MKrysz/pullup_counter/pullup_counter_code/Core/Src/images.c

#include "images.h"
#include "ssd1306.h"

#define NEEDLE_SIZE 21

/**
 * @brief 
 * 
 * @param x 
 * @param y 
 * @param image 
 */
void Image_Draw(uint8_t x, uint8_t y, image_t image)
{
    for(size_t i = 0; i<image.size; i++){
        uint8_t tempX, tempY;
        tempX = image.data[i*2];
        tempY = image.data[i*2+1];
        ssd1306_DrawPixel(x+tempX, y+tempY, White);
    }
}

void Image_Clear(uint8_t x, uint8_t y, image_t image)
{

    for(size_t i = 0; i<image.size; i++){
        uint8_t tempX, tempY;
        tempX = image.data[i*2];
        tempY = image.data[i*2+1];
        ssd1306_DrawPixel(x+tempX, y+tempY, Black);
    }
}

static const uint8_t img_meter_data[] = {
    0,26,  0,25,  0,24,  0,23,  0,22,  0,21,  1,20,  1,19,  1,18,  1,17,  2,16,  2,15,  
    2,14,  3,13,  3,12,  3,11,  4,10,  4,9,   5,8,   5,7,   6,6,   7,5,   8,5,   9,4,   
    10,4,  11,3,  12,3,  13,3,  14,2,  15,2,  16,2,  17,1,  18,1,  19,1,  20,1,  21,0, 
    22,0,  23,0,  24,0,  25,0,  26,0,  27,0,  28,0,  29,1,  30,1,  31,1,  32,1,  33,2, 
    34,2,  35,2,  36,3,  37,3,  38,3,  39,4,  40,4,  41,5,  42,5,  43,6,  44,7,  44,8,  
    45,9,  45,10, 46,11, 46,12, 46,13, 47,14, 47,15, 47,16, 48,17, 48,18, 48,19, 48,20, 
    49,21, 49,22, 49,23, 49,24, 49,25, 49,26, 23,25, 24,25, 24,24, 25,24, 25,25, 26,25,
    0,26,  1,26,  2,26,  3,26,  4,26,  5,26,  6,26,  7,26,  8,26,  9,26,  10,26, 11,26, 
    12,26, 13,26, 14,26, 15,26, 16,26, 17,26, 18,26, 19,26, 20,26, 21,26, 22,26, 23,26, 
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

        for(size_t i = 0; i<NEEDLE_SIZE; i++){
            uint8_t tempX, tempY;
            tempX = img_meter.Xsize - img_meterNeedle_data[idx][i*2];
            tempY = img_meterNeedle_data[idx][i*2+1];
            ssd1306_DrawPixel(x+tempX, y+tempY, color);
        }
    }
}

/**
 * @brief 
 * 
 * @param x 
 * @param y 
 * @param idx max 67
 */
void Image_DrawNeedle(uint8_t x, uint8_t y, size_t idx)
{
    static uint8_t last_idx = 0;

    if(idx >= 68)
        idx = 67;
        
    _DrawNeedle(x, y, last_idx, Black);
    _DrawNeedle(x, y, idx, White);
    last_idx = idx;
}
