MKrysz/pullup_counter/pullup_counter_code/Core/Src/adc.c

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
/* Includes ------------------------------------------------------------------*/
#include "adc.h"

/* USER CODE BEGIN 0 */
#include "settings.h"
/* USER CODE END 0 */

ADC_HandleTypeDef hadc1;
DMA_HandleTypeDef hdma_adc1;

/* ADC1 init function */
void MX_ADC1_Init(void)
{

  ADC_ChannelConfTypeDef sConfig = {0};

  /** Configure the global features of the ADC (Clock, Resolution, Data Alignment and number of conversion)
  */
  hadc1.Instance = ADC1;
  hadc1.Init.ClockPrescaler = ADC_CLOCK_SYNC_PCLK_DIV2;
  hadc1.Init.Resolution = ADC_RESOLUTION_12B;
  hadc1.Init.DataAlign = ADC_DATAALIGN_RIGHT;
  hadc1.Init.ScanConvMode = ADC_SCAN_ENABLE;
  hadc1.Init.EOCSelection = ADC_EOC_SEQ_CONV;
  hadc1.Init.LowPowerAutoWait = DISABLE;
  hadc1.Init.LowPowerAutoPowerOff = DISABLE;
  hadc1.Init.ContinuousConvMode = ENABLE;
  hadc1.Init.NbrOfConversion = 3;
  hadc1.Init.ExternalTrigConv = ADC_SOFTWARE_START;
  hadc1.Init.ExternalTrigConvEdge = ADC_EXTERNALTRIGCONVEDGE_NONE;
  hadc1.Init.DMAContinuousRequests = ENABLE;
  hadc1.Init.Overrun = ADC_OVR_DATA_PRESERVED;
  hadc1.Init.SamplingTimeCommon1 = ADC_SAMPLETIME_160CYCLES_5;
  hadc1.Init.SamplingTimeCommon2 = ADC_SAMPLETIME_1CYCLE_5;
  hadc1.Init.OversamplingMode = DISABLE;
  hadc1.Init.TriggerFrequencyMode = ADC_TRIGGER_FREQ_HIGH;
  if (HAL_ADC_Init(&hadc1) != HAL_OK)
  {
    Error_Handler();
  }

  /** Configure Regular Channel
  */
  sConfig.Channel = ADC_CHANNEL_0;
  sConfig.Rank = ADC_REGULAR_RANK_1;
  sConfig.SamplingTime = ADC_SAMPLINGTIME_COMMON_1;
  if (HAL_ADC_ConfigChannel(&hadc1, &sConfig) != HAL_OK)
  {
    Error_Handler();
  }

  /** Configure Regular Channel
  */
  sConfig.Channel = ADC_CHANNEL_1;
  sConfig.Rank = ADC_REGULAR_RANK_2;
  if (HAL_ADC_ConfigChannel(&hadc1, &sConfig) != HAL_OK)
  {
    Error_Handler();
  }

  /** Configure Regular Channel
  */
  sConfig.Channel = ADC_CHANNEL_VBAT;
  sConfig.Rank = ADC_REGULAR_RANK_3;
  if (HAL_ADC_ConfigChannel(&hadc1, &sConfig) != HAL_OK)
  {
    Error_Handler();
  }
}

void HAL_ADC_MspInit(ADC_HandleTypeDef* adcHandle)
{

  GPIO_InitTypeDef GPIO_InitStruct = {0};
  if(adcHandle->Instance==ADC1)
  {
    /* ADC1 clock enable */
    __HAL_RCC_ADC_CLK_ENABLE();

    __HAL_RCC_GPIOA_CLK_ENABLE();
    /**ADC1 GPIO Configuration
    PA0     ------> ADC1_IN0
    PA1     ------> ADC1_IN1
    */
    GPIO_InitStruct.Pin = PROX_OUT_Pin|BAT_RAW_Pin;
    GPIO_InitStruct.Mode = GPIO_MODE_ANALOG;
    GPIO_InitStruct.Pull = GPIO_NOPULL;
    HAL_GPIO_Init(GPIOA, &GPIO_InitStruct);

    /* ADC1 DMA Init */
    /* ADC1 Init */
    hdma_adc1.Instance = DMA1_Channel2;
    hdma_adc1.Init.Request = DMA_REQUEST_ADC1;
    hdma_adc1.Init.Direction = DMA_PERIPH_TO_MEMORY;
    hdma_adc1.Init.PeriphInc = DMA_PINC_DISABLE;
    hdma_adc1.Init.MemInc = DMA_MINC_ENABLE;
    hdma_adc1.Init.PeriphDataAlignment = DMA_PDATAALIGN_WORD;
    hdma_adc1.Init.MemDataAlignment = DMA_MDATAALIGN_WORD;
    hdma_adc1.Init.Mode = DMA_CIRCULAR;
    hdma_adc1.Init.Priority = DMA_PRIORITY_LOW;
    if (HAL_DMA_Init(&hdma_adc1) != HAL_OK)
    {
      Error_Handler();
    }

    __HAL_LINKDMA(adcHandle,DMA_Handle,hdma_adc1);

  }
}

void HAL_ADC_MspDeInit(ADC_HandleTypeDef* adcHandle)
{

  if(adcHandle->Instance==ADC1)
  {
    /* Peripheral clock disable */
    __HAL_RCC_ADC_CLK_DISABLE();

    /**ADC1 GPIO Configuration
    PA0     ------> ADC1_IN0
    PA1     ------> ADC1_IN1
    */
    HAL_GPIO_DeInit(GPIOA, PROX_OUT_Pin|BAT_RAW_Pin);

    /* ADC1 DMA DeInit */
    HAL_DMA_DeInit(adcHandle->DMA_Handle);
  }
}

/* USER CODE BEGIN 1 */

uint32_t ambientDistance = 0;

/**
 * [0] - Poximity
 * [1] - Battery
 * [2] - Backup battery
 */
uint32_t ADC_buffer[3];

void ADC_Init()
{
  HAL_ADC_Start_DMA(&hadc1, ADC_buffer, 3);
}


/**
 * @brief returns relative reading from proximity sensor
 * 
 * @return uint32_t differnce between ambient and current voltage
 */
int32_t ADC_MeasureDistance()
{
  uint32_t raw = ADC_buffer[0];
  return (int32_t) (raw - ambientDistance);
  // return raw;
}

/**
 * @brief recalibrates ambient value
 * 
 */
void ADC_DistanceCalibrate()
{
  const size_t bufferSize = 64;
  uint32_t result = 0;
  HAL_GPIO_WritePin(PROX_EN_GPIO_Port, PROX_EN_Pin, 1);
  HAL_Delay(100);
  for (size_t i = 0; i < bufferSize; i++){
    HAL_Delay(2);
    result += ADC_buffer[0];
  }
  HAL_GPIO_WritePin(PROX_EN_GPIO_Port, PROX_EN_Pin, 0);
  ambientDistance = result>>6;
}

/**
 * @brief 
 * 
 * @return uint32_t battery voltage in mV
 */
uint32_t ADC_MeasureBattery()
{
  return ((ADC_buffer[1])*ADC_VCC)>>ADC_RES;
}

/**
 * @brief 
 * 
 * @return uint32_t backup battery voltage in mV
 */
uint32_t ADC_MeasureBackupBattery()
{
  return ((ADC_buffer[2])*ADC_VCC)>>ADC_RES;
}

void ADC_PROX_ON()
{
  flags.IsProxOn = true;
  HAL_GPIO_WritePin(PROX_EN_GPIO_Port, PROX_EN_Pin, 1);
}

void ADC_PROX_OFF()
{
  flags.IsProxOn = false;
  HAL_GPIO_WritePin(PROX_EN_GPIO_Port, PROX_EN_Pin, 0);
}

/* USER CODE END 1 */
