MKrysz/pullup_counter/pullup_counter_code/Core/Inc/config.h

#ifndef _CONFIG_H
#define _CONFIG_H

// shutdown and sleep are mutually exlusive
#define SHUTDOWN_ENABLE
// #define SLEEP_ENABLE

// programming routine
#define PROGRAM_ROUTINE
// programming routine - options 
#define SET_RTC
// #define ERASE_FLASH
// #define RESET_SETTINGS
// #define RESET_EEPROM



#endif
