MKrysz/pullup_counter/pullup_counter_code/Core/Src/rtc.c

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
/* Includes ------------------------------------------------------------------*/
#include "rtc.h"

/* USER CODE BEGIN 0 */
#include <stdio.h>
#include "compileTime.h"
/* USER CODE END 0 */

RTC_HandleTypeDef hrtc;

/* RTC init function */
void MX_RTC_Init(void)
{

  RTC_TimeTypeDef sTime = {0};
  RTC_DateTypeDef sDate = {0};

  /** Initialize RTC Only
  */
  hrtc.Instance = RTC;
  hrtc.Init.HourFormat = RTC_HOURFORMAT_24;
  hrtc.Init.AsynchPrediv = 127;
  hrtc.Init.SynchPrediv = 255;
  hrtc.Init.OutPut = RTC_OUTPUT_DISABLE;
  hrtc.Init.OutPutRemap = RTC_OUTPUT_REMAP_NONE;
  hrtc.Init.OutPutPolarity = RTC_OUTPUT_POLARITY_HIGH;
  hrtc.Init.OutPutType = RTC_OUTPUT_TYPE_OPENDRAIN;
  hrtc.Init.OutPutPullUp = RTC_OUTPUT_PULLUP_NONE;
  if (HAL_RTC_Init(&hrtc) != HAL_OK)
  {
    Error_Handler();
  }

  /** Initialize RTC and set the Time and Date
  */
  sTime.Hours = 0x0;
  sTime.Minutes = 0x0;
  sTime.Seconds = 0x0;
  sTime.SubSeconds = 0x0;
  sTime.DayLightSaving = RTC_DAYLIGHTSAVING_NONE;
  sTime.StoreOperation = RTC_STOREOPERATION_RESET;
  if (HAL_RTC_SetTime(&hrtc, &sTime, RTC_FORMAT_BCD) != HAL_OK)
  {
    Error_Handler();
  }
  sDate.WeekDay = RTC_WEEKDAY_MONDAY;
  sDate.Month = RTC_MONTH_JANUARY;
  sDate.Date = 0x1;
  sDate.Year = 0x0;

  if (HAL_RTC_SetDate(&hrtc, &sDate, RTC_FORMAT_BCD) != HAL_OK)
  {
    Error_Handler();
  }
}

void HAL_RTC_MspInit(RTC_HandleTypeDef* rtcHandle)
{

  RCC_PeriphCLKInitTypeDef PeriphClkInit = {0};
  if(rtcHandle->Instance==RTC)
  {
  /** Initializes the peripherals clocks
  */
    PeriphClkInit.PeriphClockSelection = RCC_PERIPHCLK_RTC;
    PeriphClkInit.RTCClockSelection = RCC_RTCCLKSOURCE_HSE_DIV32;

    if (HAL_RCCEx_PeriphCLKConfig(&PeriphClkInit) != HAL_OK)
    {
      Error_Handler();
    }

    /* RTC clock enable */
    __HAL_RCC_RTC_ENABLE();
    __HAL_RCC_RTCAPB_CLK_ENABLE();
  }
}

void HAL_RTC_MspDeInit(RTC_HandleTypeDef* rtcHandle)
{

  if(rtcHandle->Instance==RTC)
  {
    /* Peripheral clock disable */
    __HAL_RCC_RTC_DISABLE();
    __HAL_RCC_RTCAPB_CLK_DISABLE();
  }
}

/* USER CODE BEGIN 1 */

RTC_DateTypeDef sDate = {0};
RTC_TimeTypeDef sTime = {0};

/**
 * @brief converts HAL's weekday to a readable strings
 * 
 * @param weekday int from 1 to 7 where 1 is Monday and 7 is Saturday
 * @param dst string with a size of at least 12 in witch return value will be written to
 * 
 * @returns nr of characters written
 */
int RTC_WeekDay2String(uint8_t weekday, char* dst)
{
  char truthTable[7][12] = {
    "Monday",
    "Tuesday",
    "Wednesday",
    "Thursday",
    "Friday",
    "Saturday",
    "Sunday"
  };
  size_t i;
  for(i = 0; truthTable[weekday-1][i] != '\0'; i++){
    dst[i] = truthTable[weekday-1][i];
  }
  dst[i] = 0;
  return i;
}

/**
 * @brief prints current time and date from RTC
 * 
 */
int RTC_ToString(char *dst)
{
  size_t i = 0;

  i += sprintf(dst+i, "%u:%u:%u\n", 
    sTime.Hours, sTime.Minutes, sTime.Seconds);
  
  i += sprintf(dst+i, "%u/%u/20%u\n",
    sDate.Date, sDate.Month, sDate.Year);

  i += sprintf(dst, "Weekday = ");

  i += RTC_WeekDay2String(sDate.WeekDay, dst);
  return i;
}

/**
 * @brief sets RTC time and date to compile time and date
 * 
 */
void RTC_SetCurrentTime()
{
  sDate.Date = __TIME_DAYS__;
  sDate.Month = __TIME_MONTH__;
  sDate.Year = __TIME_YEARS__ - 2000;
  sDate.WeekDay = RTC_WEEKDAY_WEDNESDAY;
  HAL_RTC_SetDate(&hrtc, &sDate, FORMAT_BIN);

  sTime.Hours = __TIME_HOURS__;
  sTime.Minutes = __TIME_MINUTES__;
  sTime.Seconds = __TIME_SECONDS__;
  HAL_RTC_SetTime(&hrtc, &sTime, FORMAT_BIN);
}

/**
 * @brief reads current time and date from RTC and stores result in global sTime and sDate variables
 * 
 */
void RTC_ReadTime()
{
  HAL_RTC_GetTime(&hrtc, &sTime, RTC_FORMAT_BIN);
  HAL_RTC_GetDate(&hrtc, &sDate, RTC_FORMAT_BIN);
}
/* USER CODE END 1 */
